SPIvSPI/dc27sao/img/erc-the-hard-way.jpg

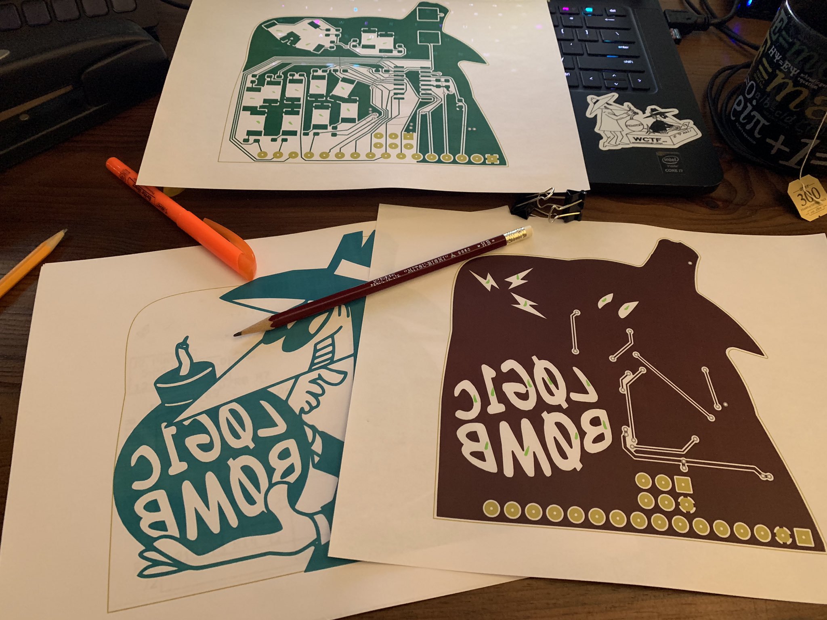
img/erc-the-hard-way.jpg
