SPIvSPI/dc27sao/img/ghetto-reflo-controller.jpg

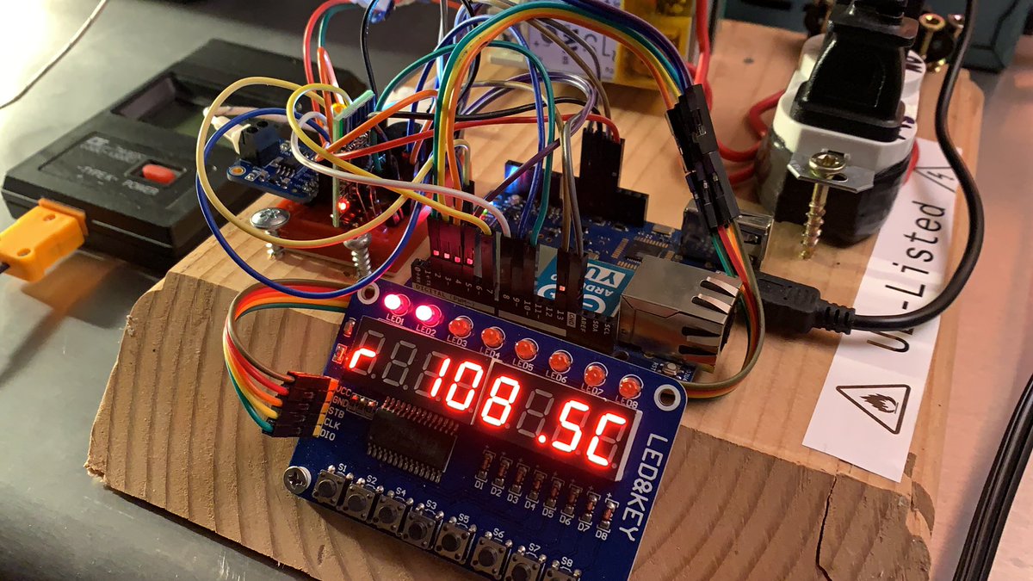
img/ghetto-reflo-controller.jpg
