SPIvSPI/dc27sao/img/panelizing-reels.jpg

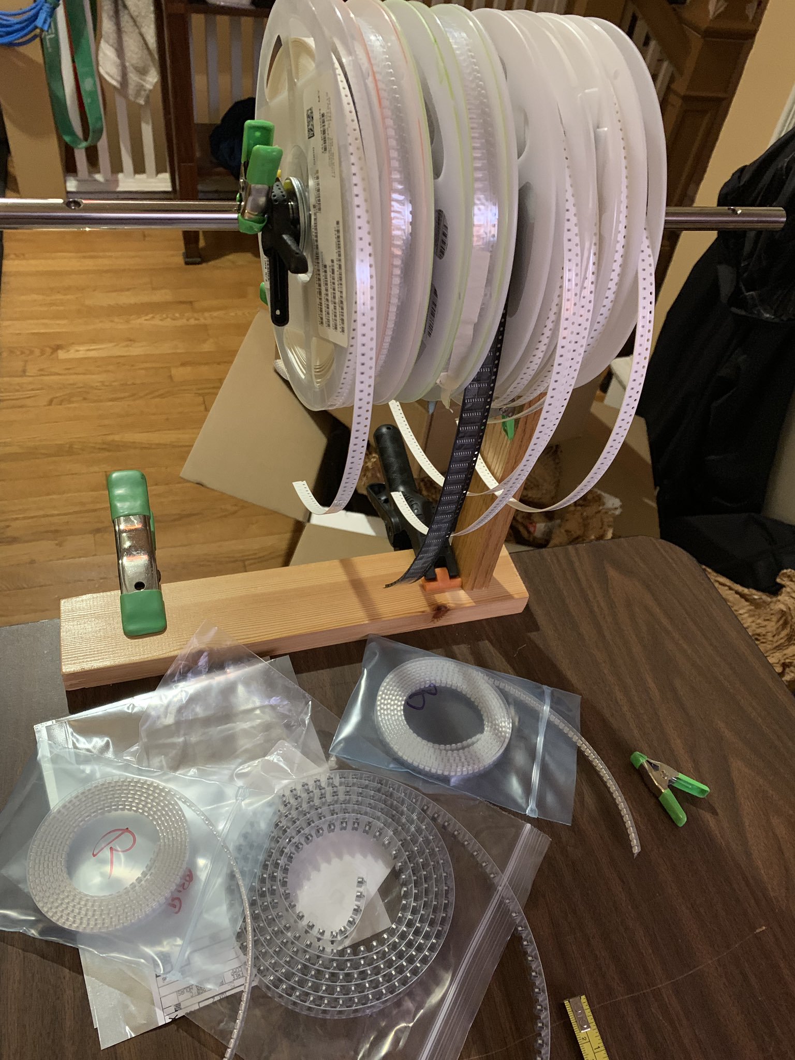
img/panelizing-reels.jpg
