SPIvSPI/dc27sao/img/spivspi.jpg

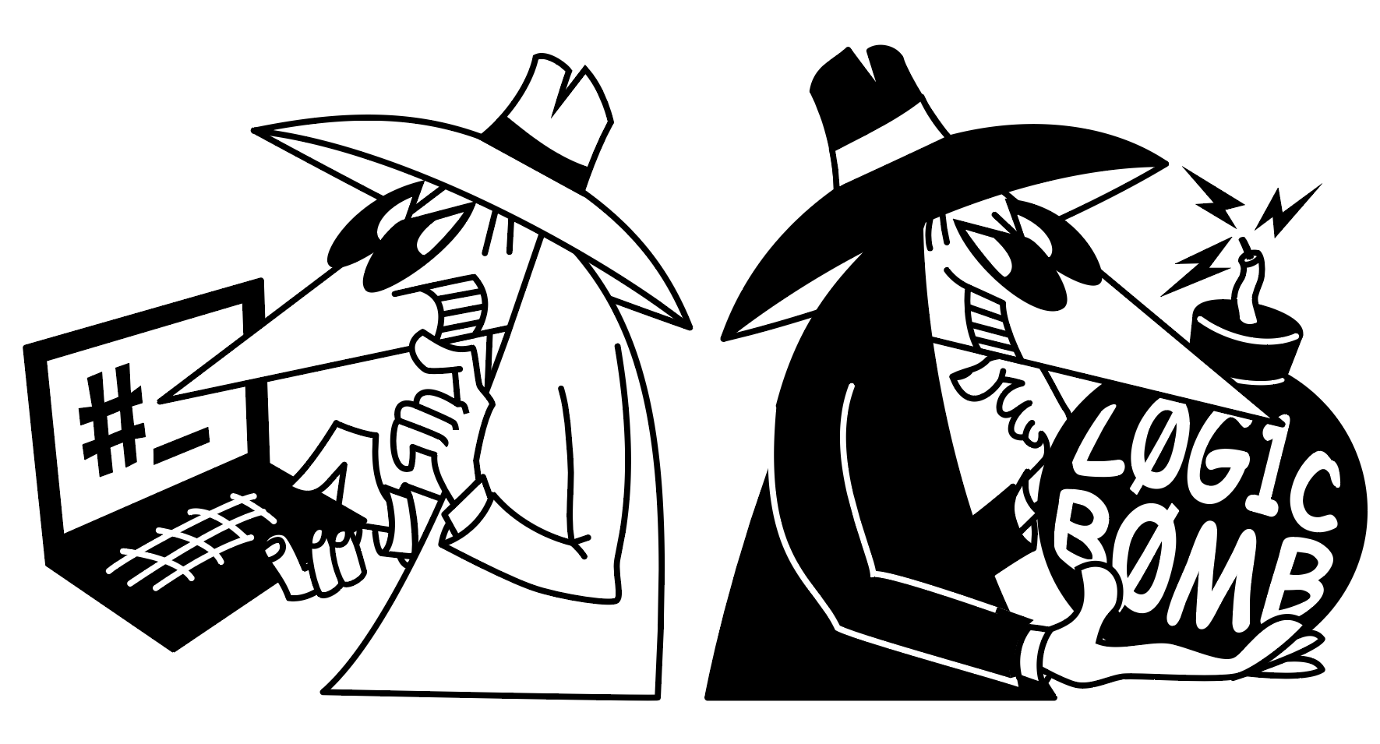
img/spivspi.jpg
