SPIvSPI/dc27sao/img/ul-listed.jpg

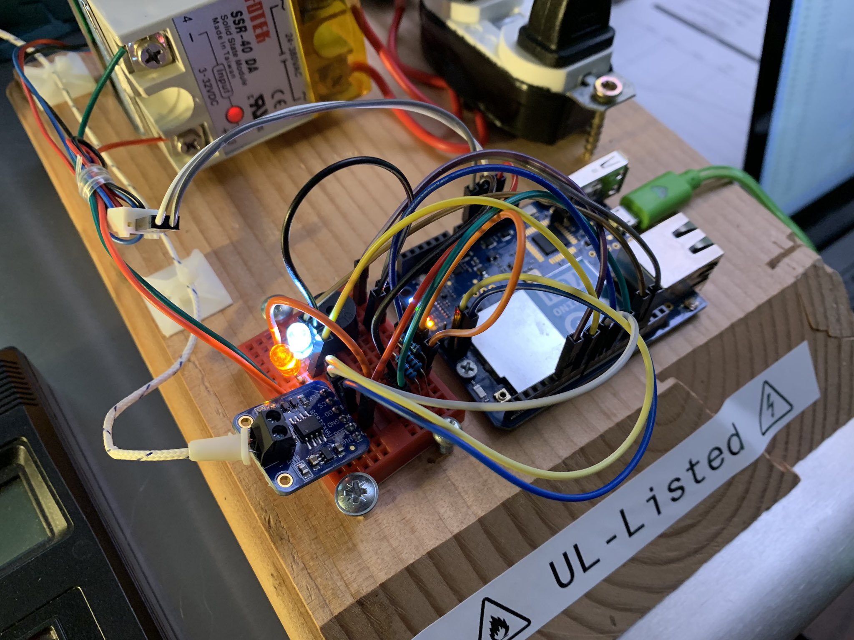
img/ul-listed.jpg
