SPIvSPI/dc27sao/img/debug-jig.jpg

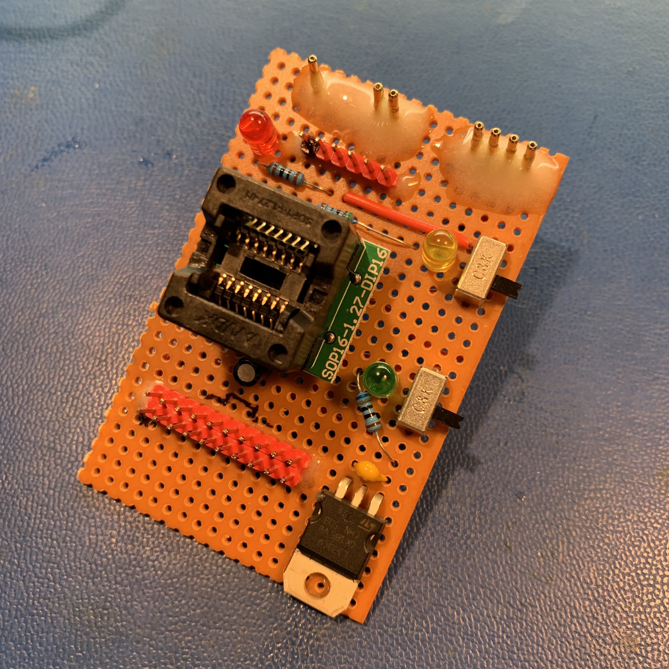
img/debug-jig.jpg
